deqit/PhilipsPM2528/Data/Fotos (JosVanDijken)/AC AMPLIFIER N24 (4022 325 7917.3).jpg

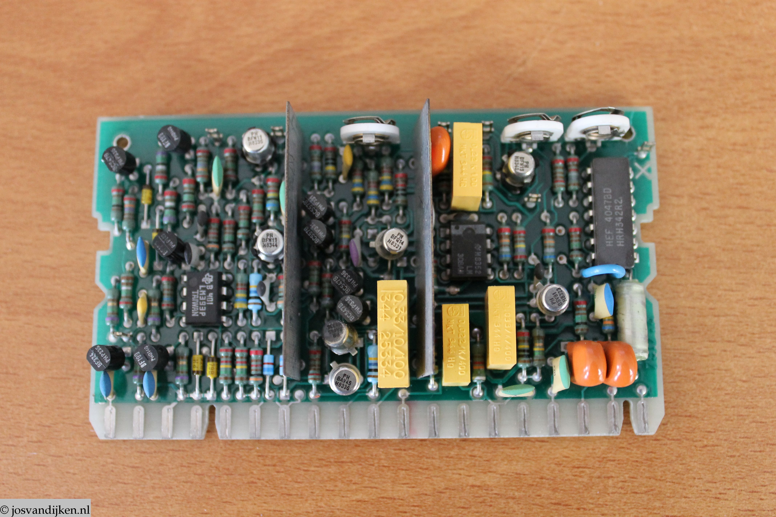
Data/Fotos (JosVanDijken)/AC AMPLIFIER N24 (4022 325 7917.3).jpg
