deqit/PhilipsPM2528/Data/Fotos (JosVanDijken)/ADC ANALOG N21 (4022 325 7911.3).jpg

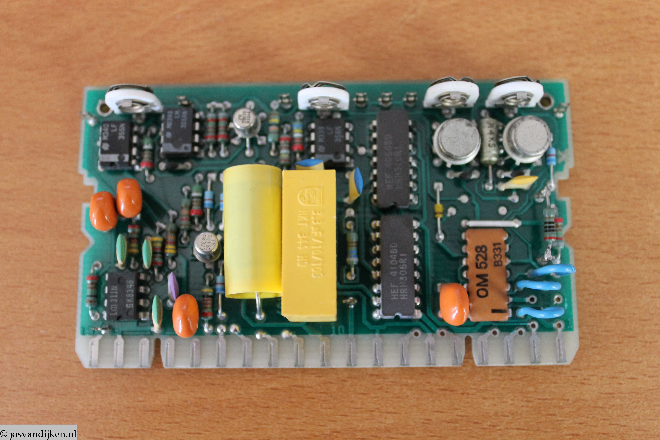
Data/Fotos (JosVanDijken)/ADC ANALOG N21 (4022 325 7911.3).jpg
