deqit/PhilipsPM2528/Data/Fotos (JosVanDijken)/ADC CONTROL N20 (4022 325 7909.4).jpg

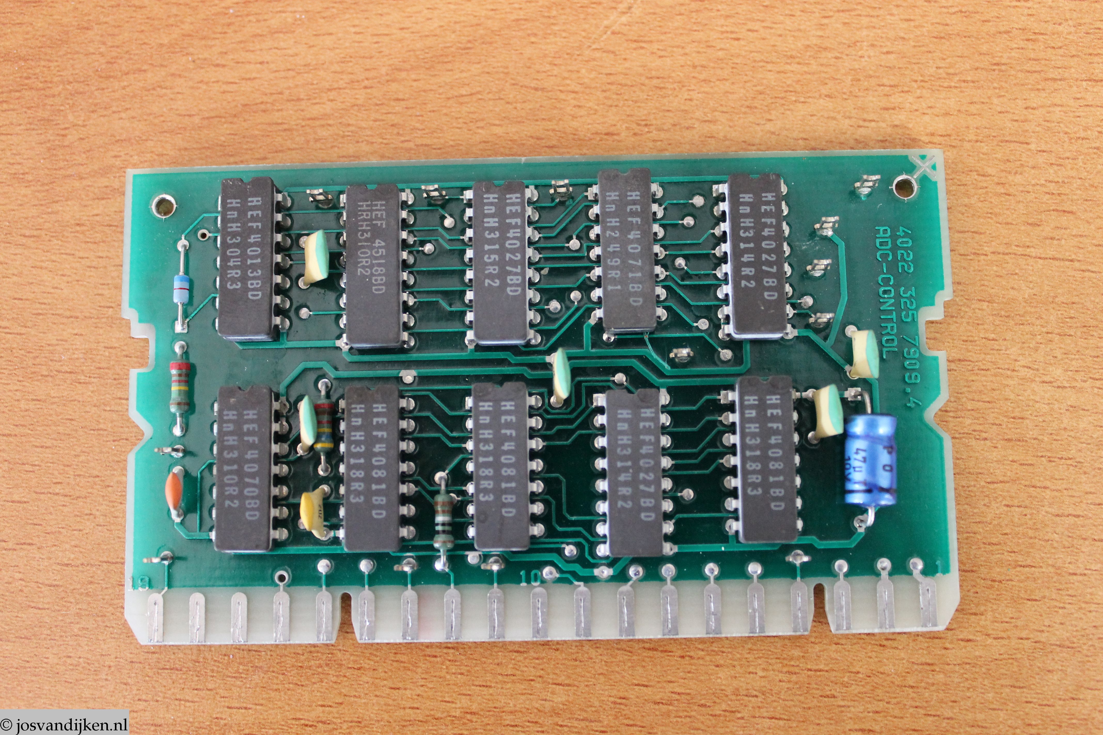
Data/Fotos (JosVanDijken)/ADC CONTROL N20 (4022 325 7909.4).jpg
