deqit/PhilipsPM2528/Data/Fotos (JosVanDijken)/CURRENT SOURCE N23.jpg

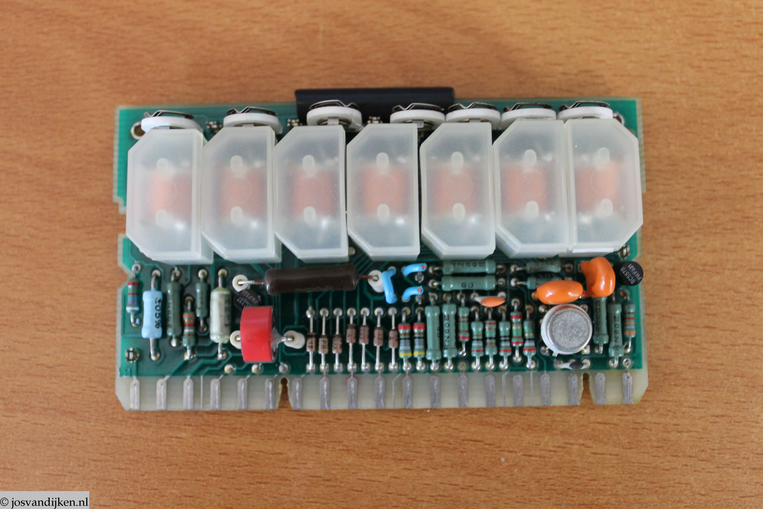
Data/Fotos (JosVanDijken)/CURRENT SOURCE N23.jpg
