deqit/PhilipsPM2528/Data/Fotos (JosVanDijken)/DC AMPLIFIER N22 (4022 325 7913.4).jpg

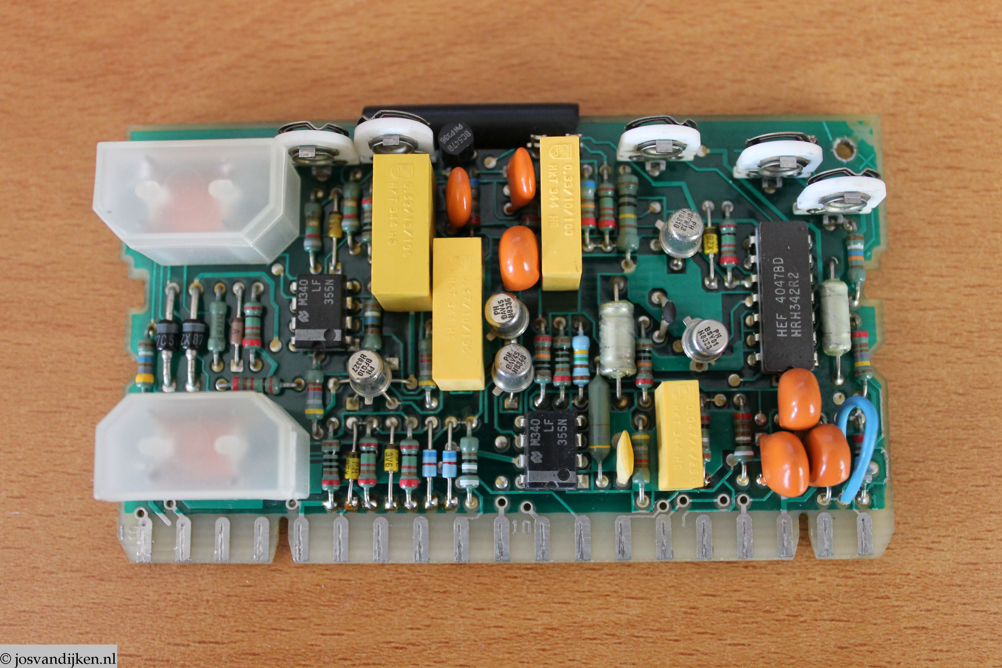
Data/Fotos (JosVanDijken)/DC AMPLIFIER N22 (4022 325 7913.4).jpg
