deqit/PhilipsPM2528/Data/Fotos (JosVanDijken)/GALVANIC SEPERATION N30 (4022 325 7927.3).jpg

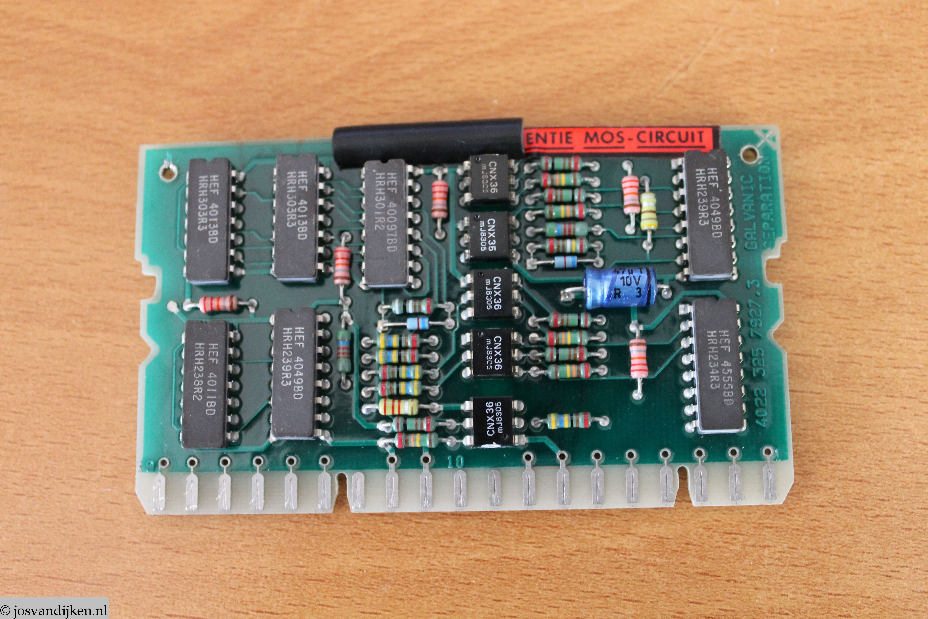
Data/Fotos (JosVanDijken)/GALVANIC SEPERATION N30 (4022 325 7927.3).jpg
