deqit/PhilipsPM2528/Data/Fotos (JosVanDijken)/IEC INTERFACE PM9291(4022 325 7931.4)_back.jpg

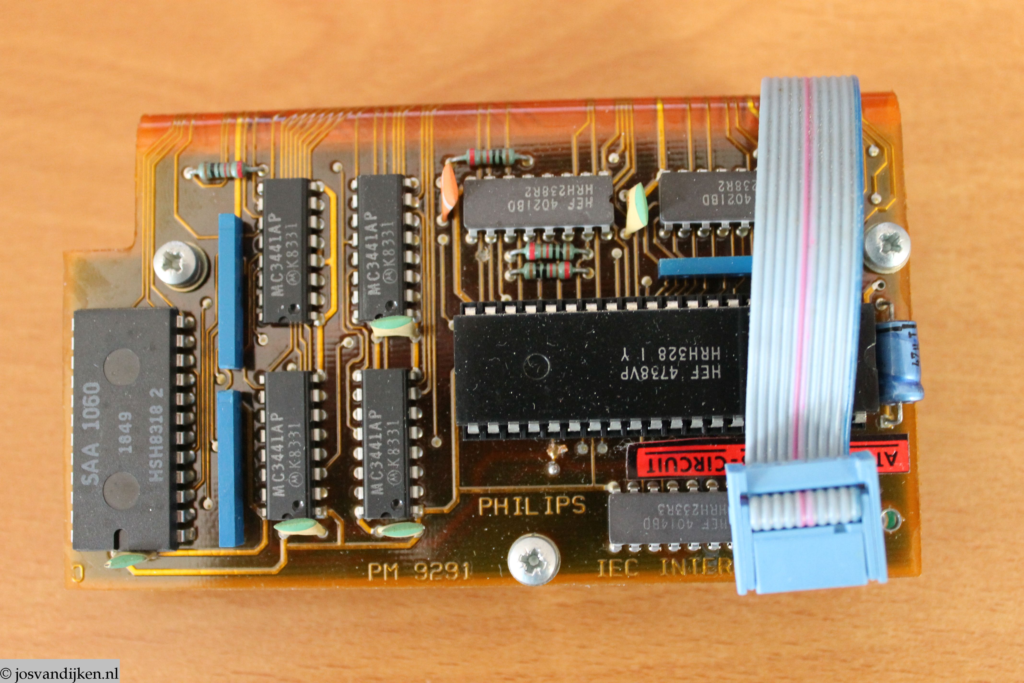
Data/Fotos (JosVanDijken)/IEC INTERFACE PM9291(4022 325 7931.4)_back.jpg
