deqit/PhilipsPM2528/Data/Fotos (JosVanDijken)/IMG_6188.jpg

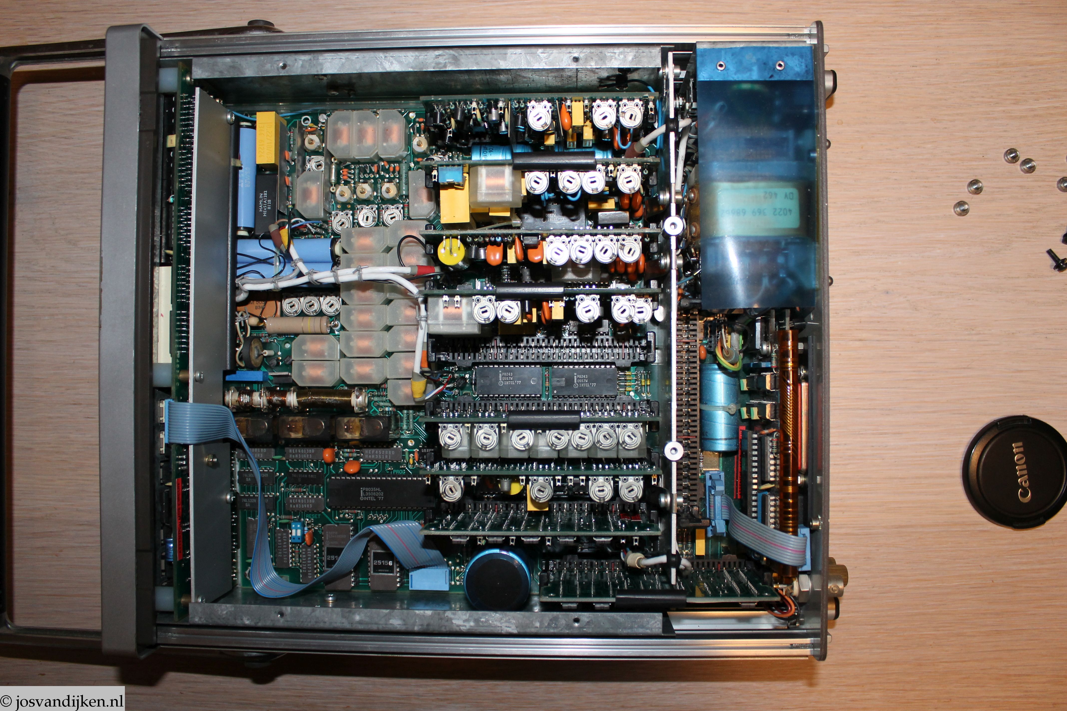
Data/Fotos (JosVanDijken)/IMG_6188.jpg
