deqit/PhilipsPM2528/Data/Fotos (JosVanDijken)/MOTHERBOARD N1 (4022 325 7907.4).jpg

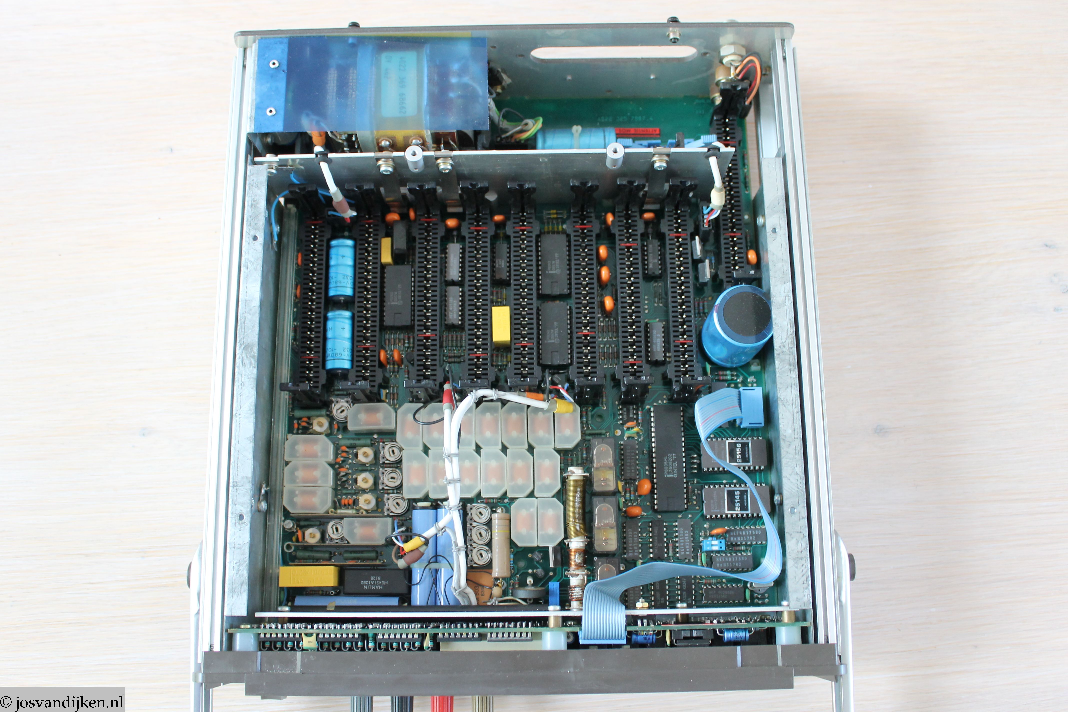
Data/Fotos (JosVanDijken)/MOTHERBOARD N1 (4022 325 7907.4).jpg
