deqit/PhilipsPM2528/Data/Fotos (JosVanDijken)/PEAKDETECTOR PM9259 N27 (4022 325 7923.3).jpg

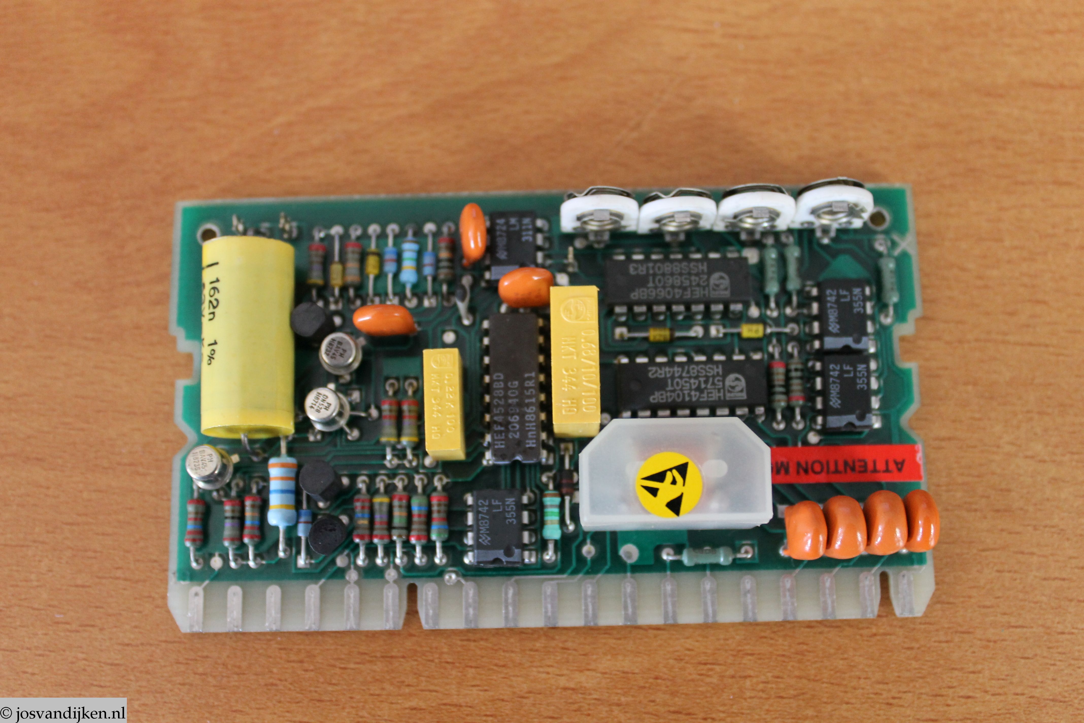
Data/Fotos (JosVanDijken)/PEAKDETECTOR PM9259 N27 (4022 325 7923.3).jpg
