deqit/PhilipsPM2528/Data/Fotos (JosVanDijken)/RMS CONVERTER N25.jpg

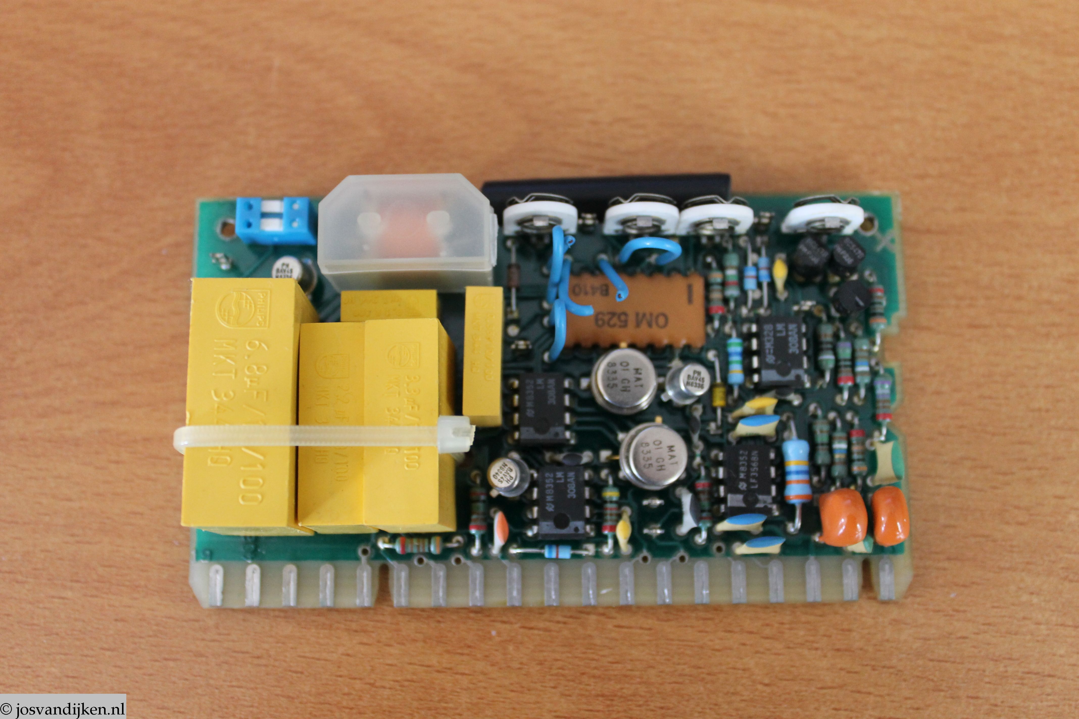
Data/Fotos (JosVanDijken)/RMS CONVERTER N25.jpg
