deqit/PhilipsPM2528/Data/Documentation/Components/BFQ10.pdf

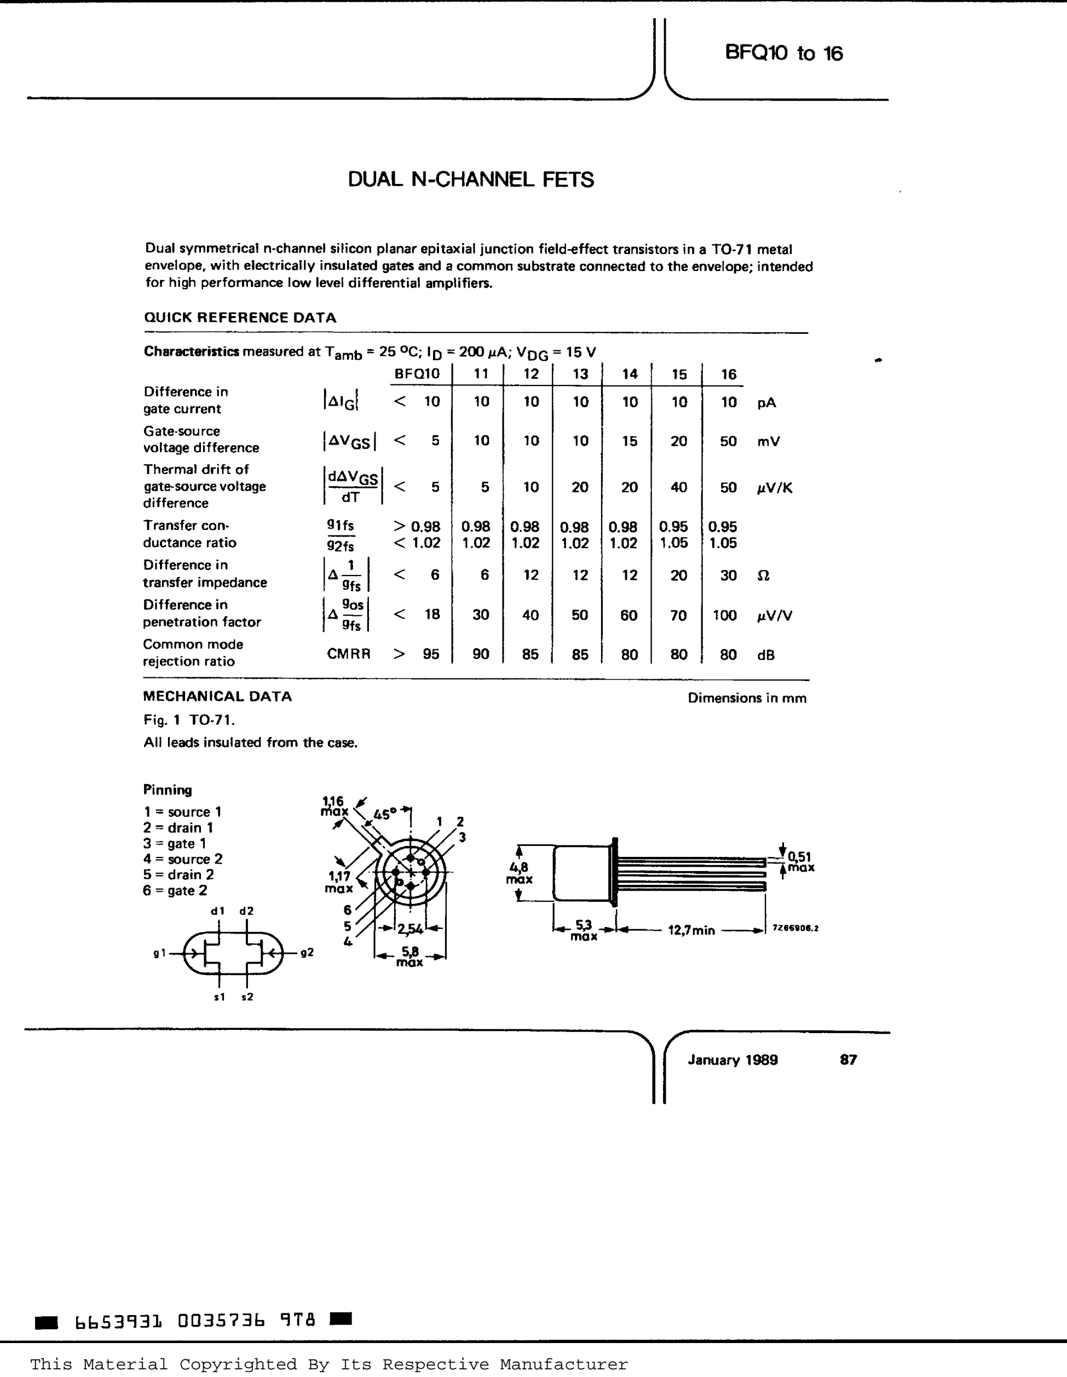
[picture p66: page 1]

This Material Copyrighted By Its Respective Manufacturer

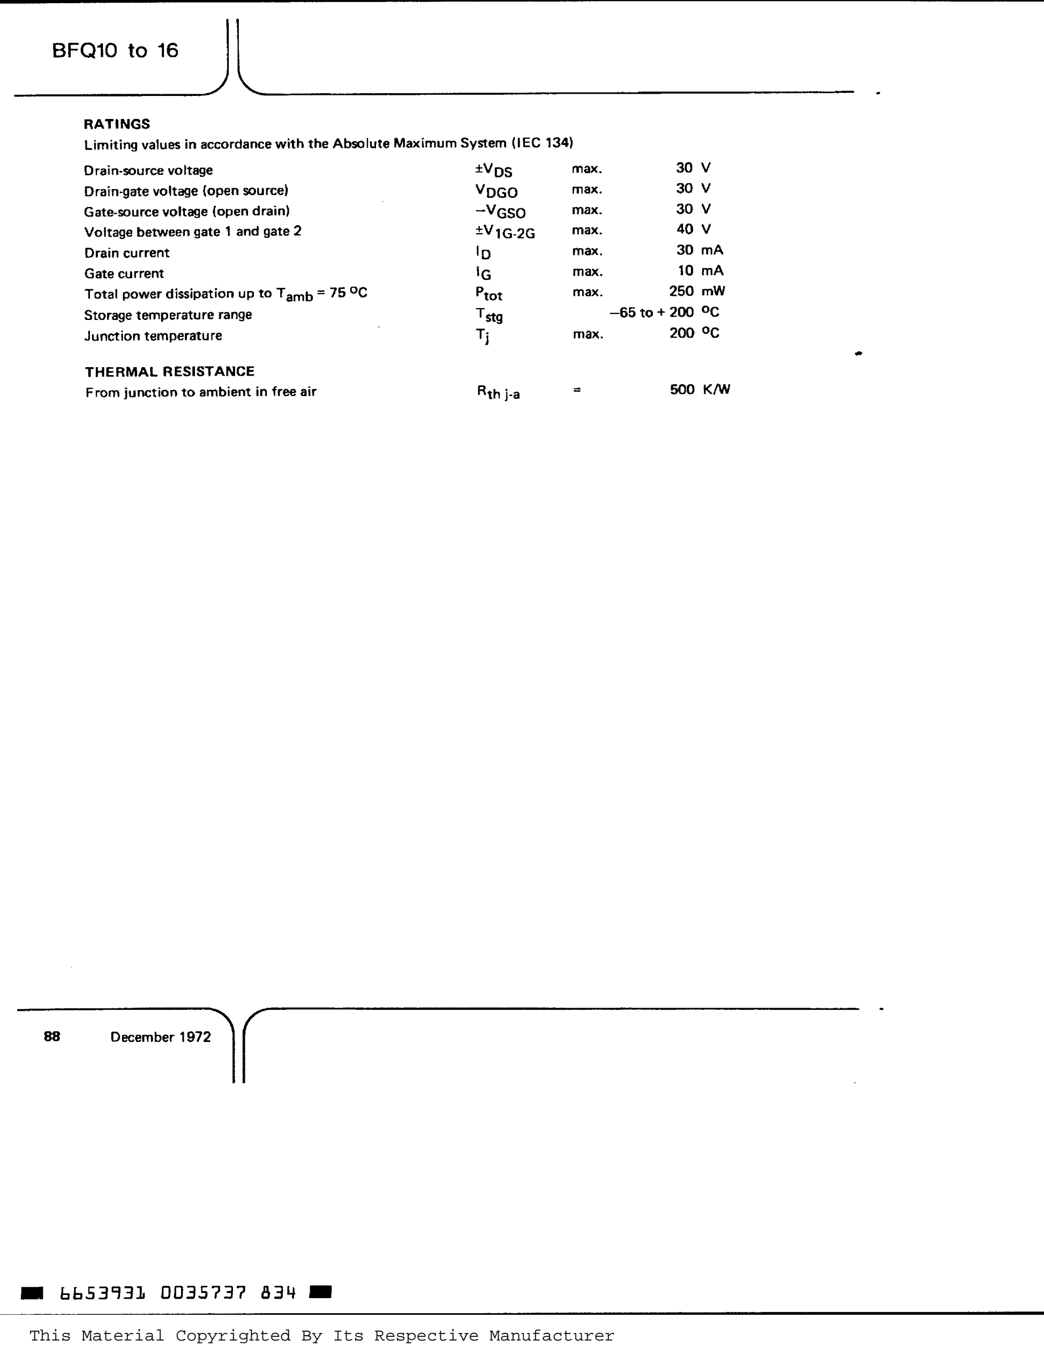
[picture p67: page 2]
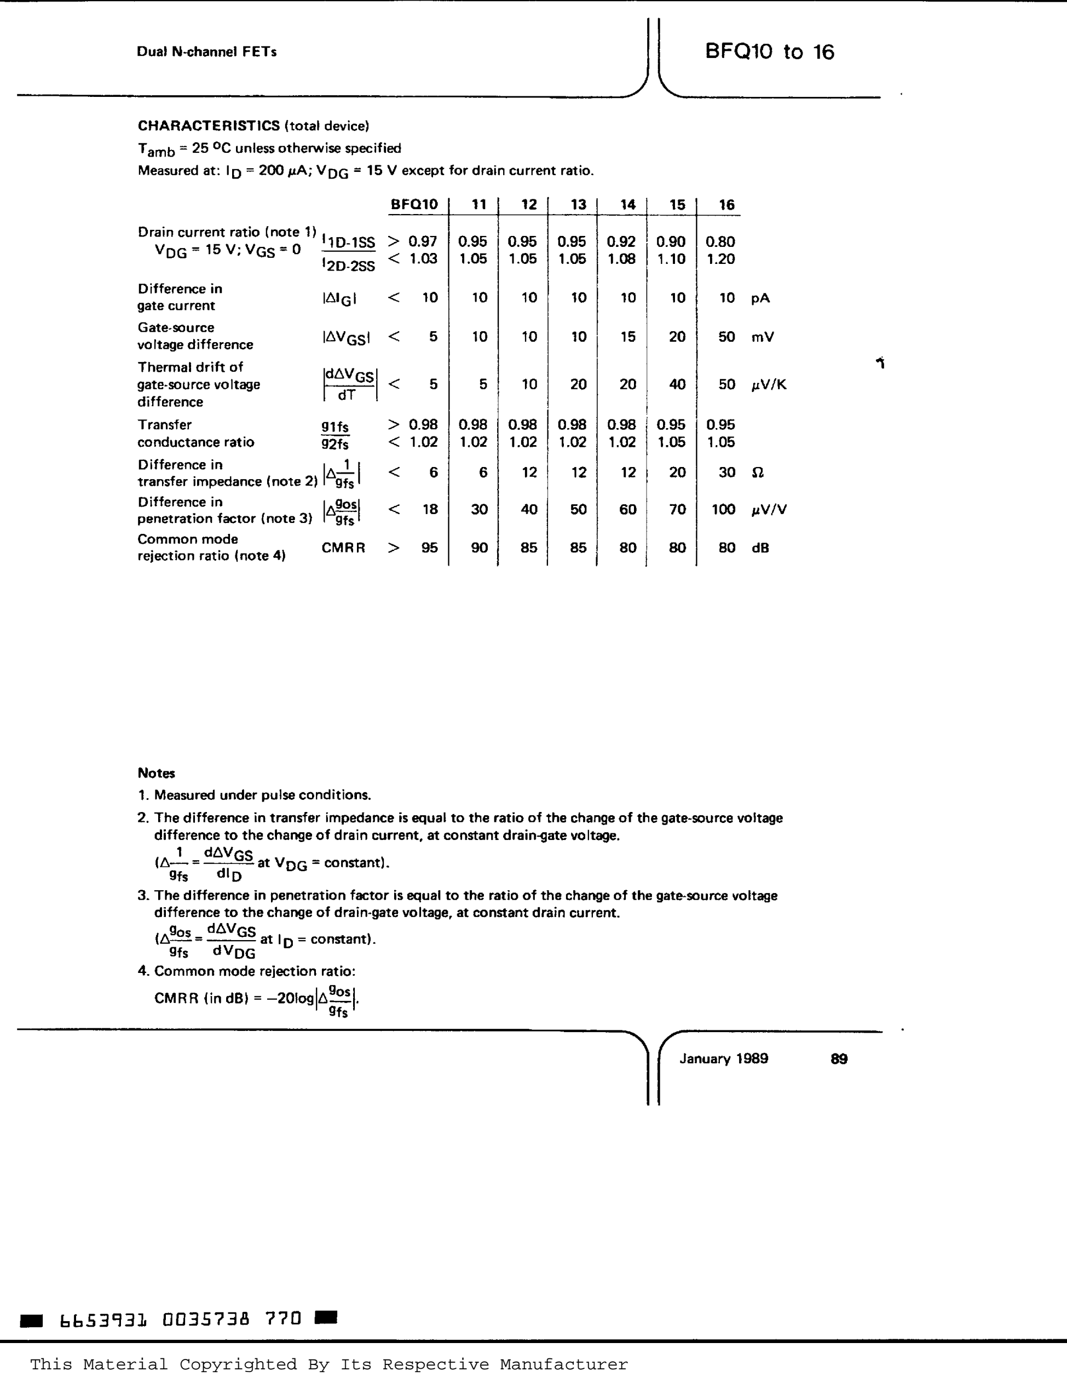
[picture p68: page 3]
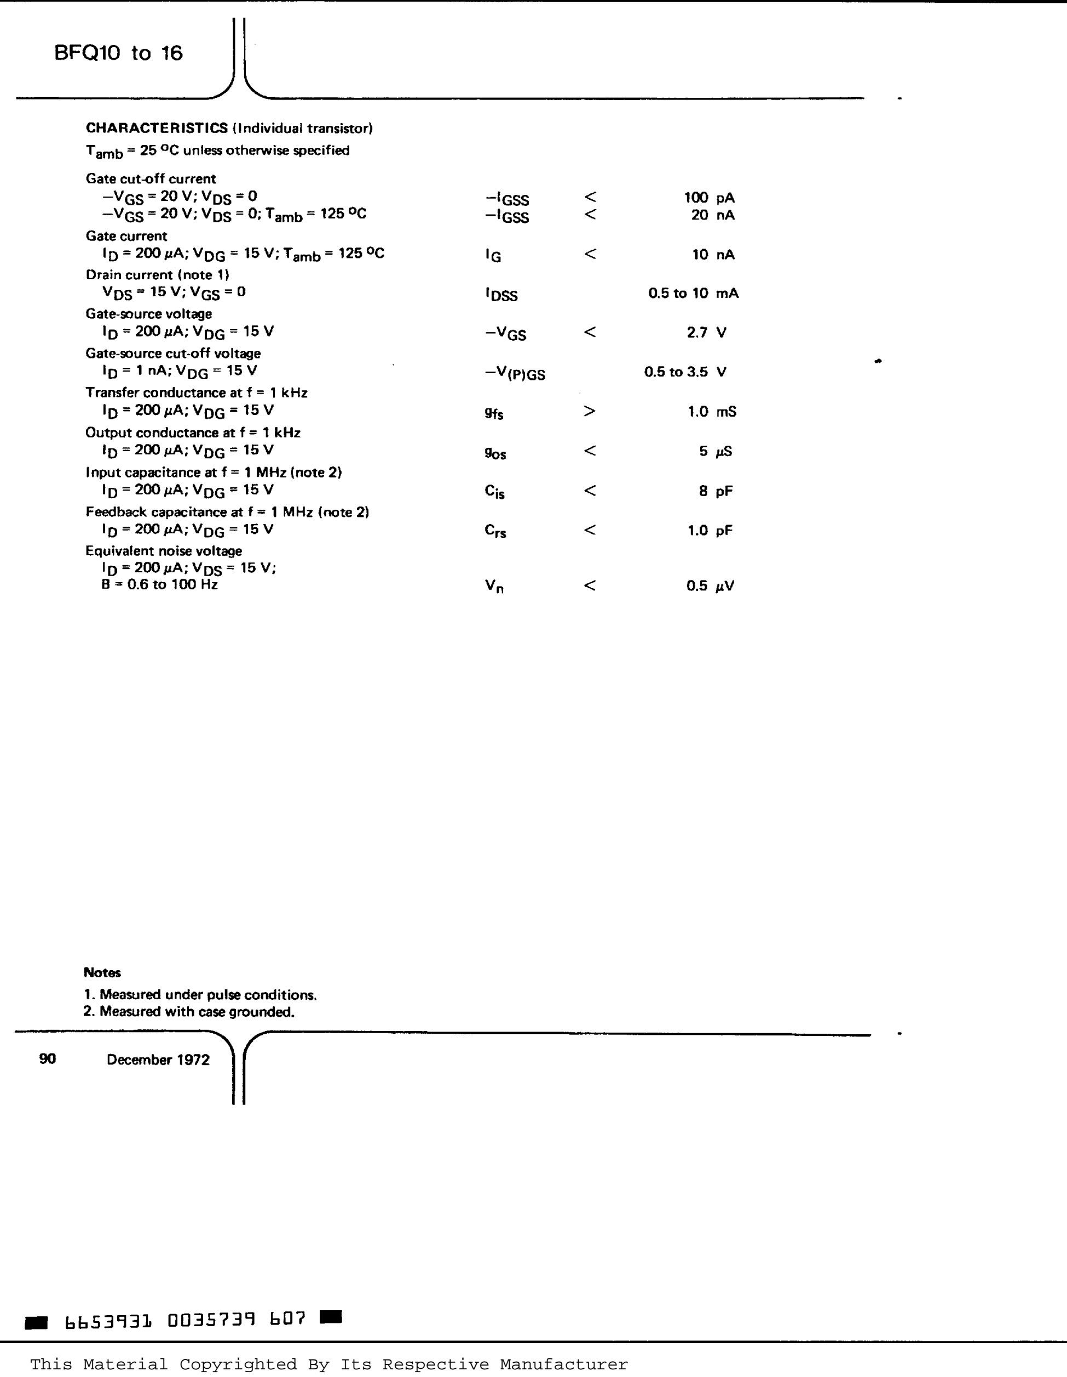
[picture p69: page 4]
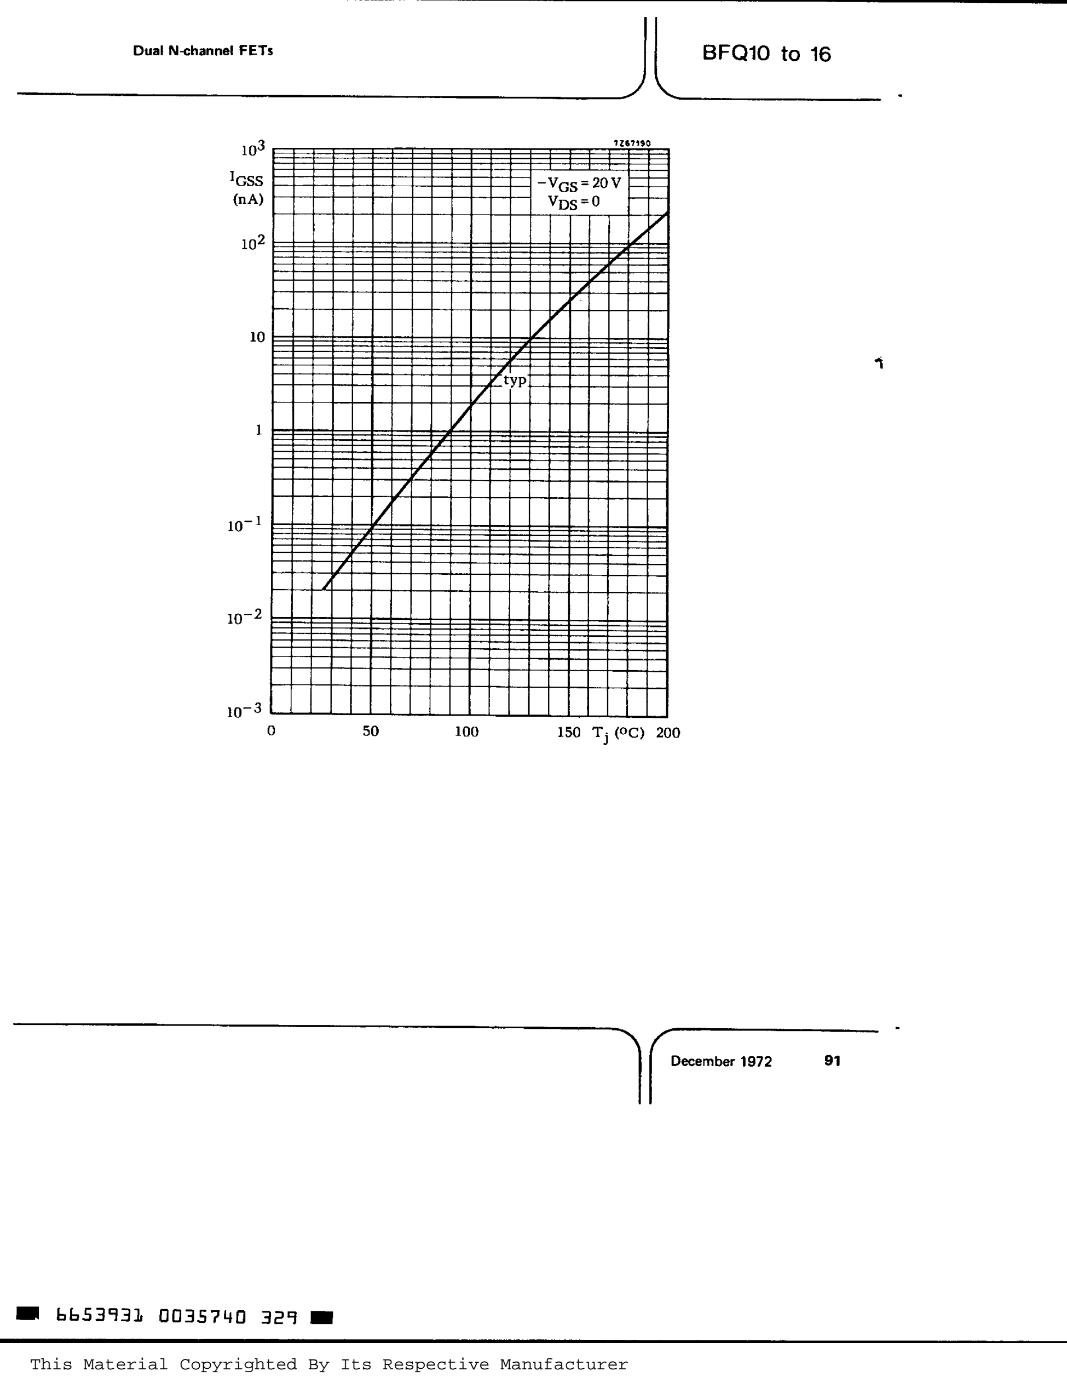
[picture p70: page 5]
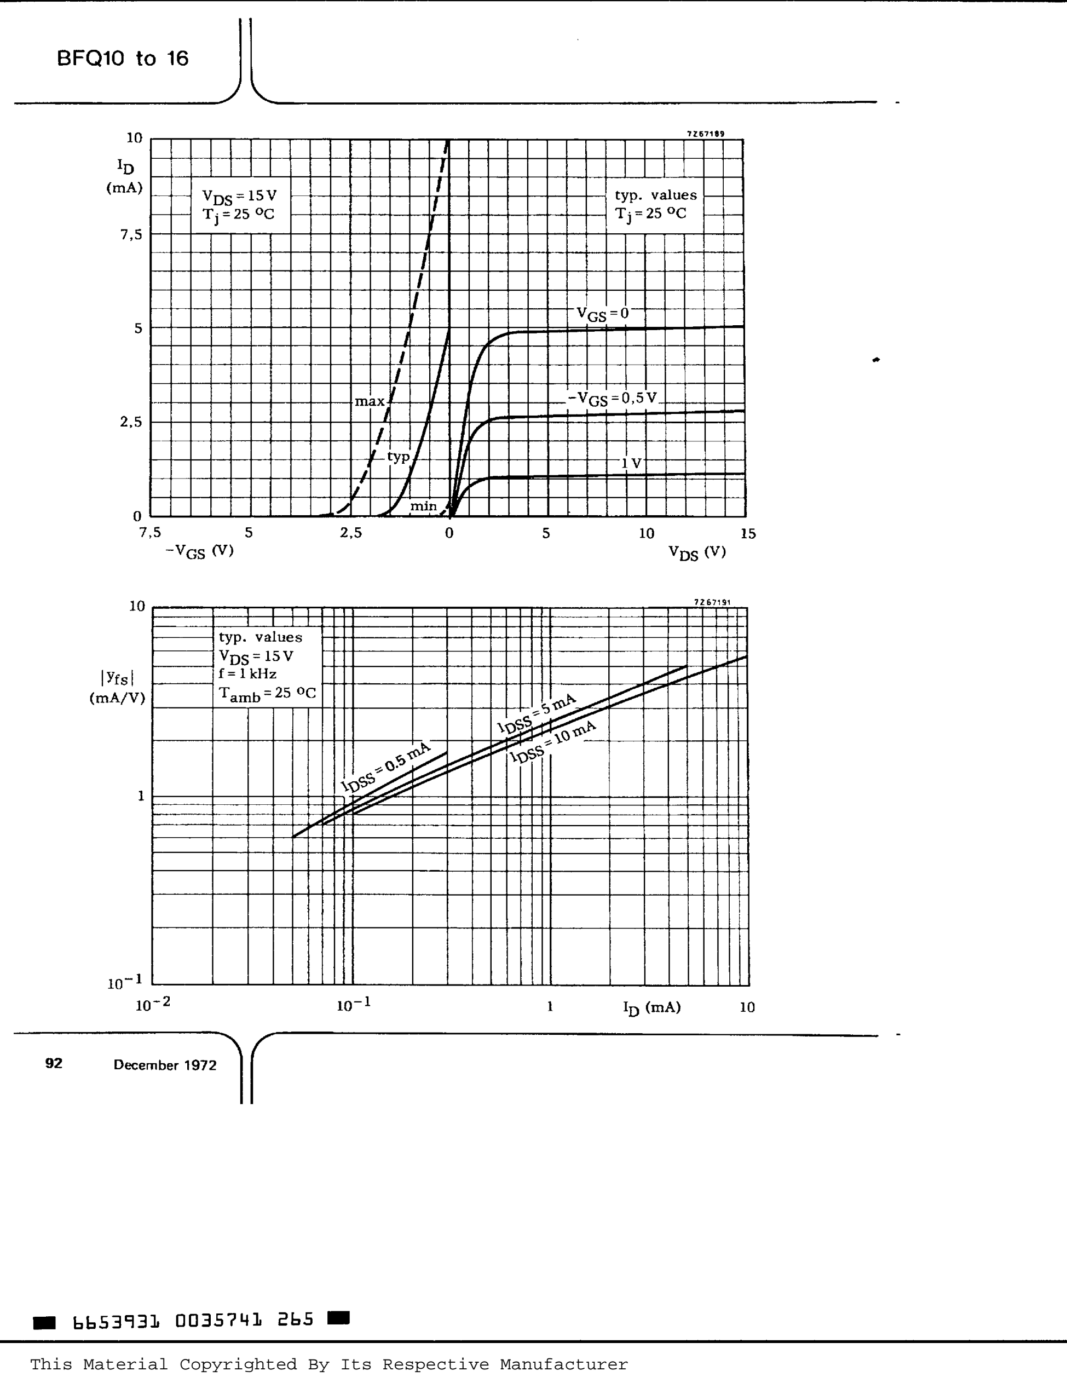
[picture p71: page 6]
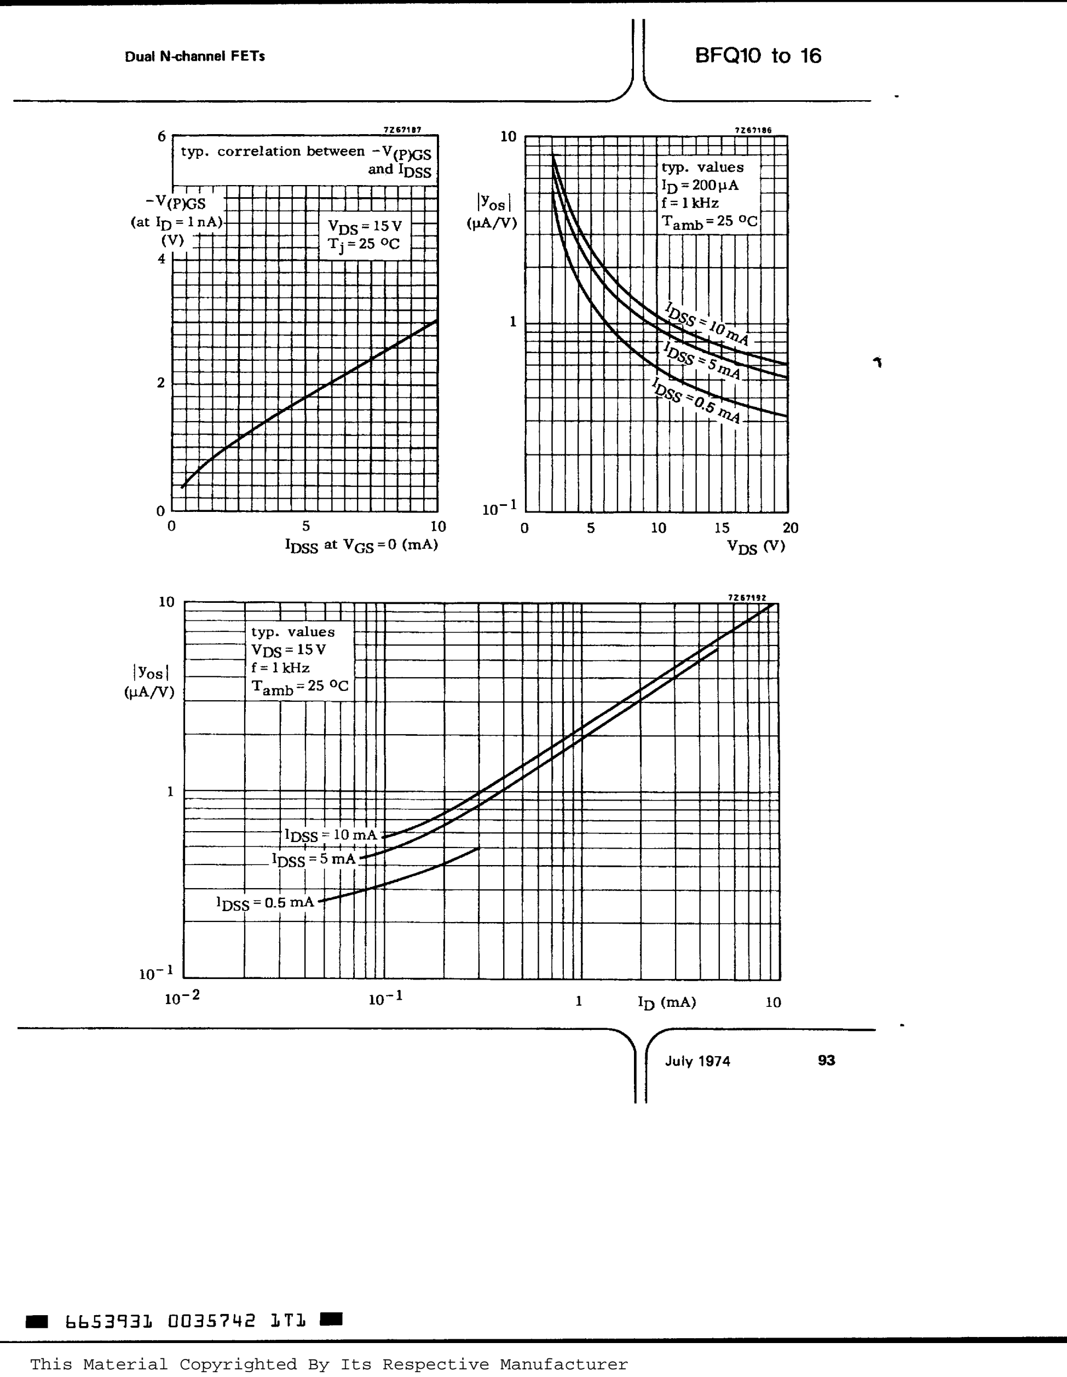
[picture p72: page 7]
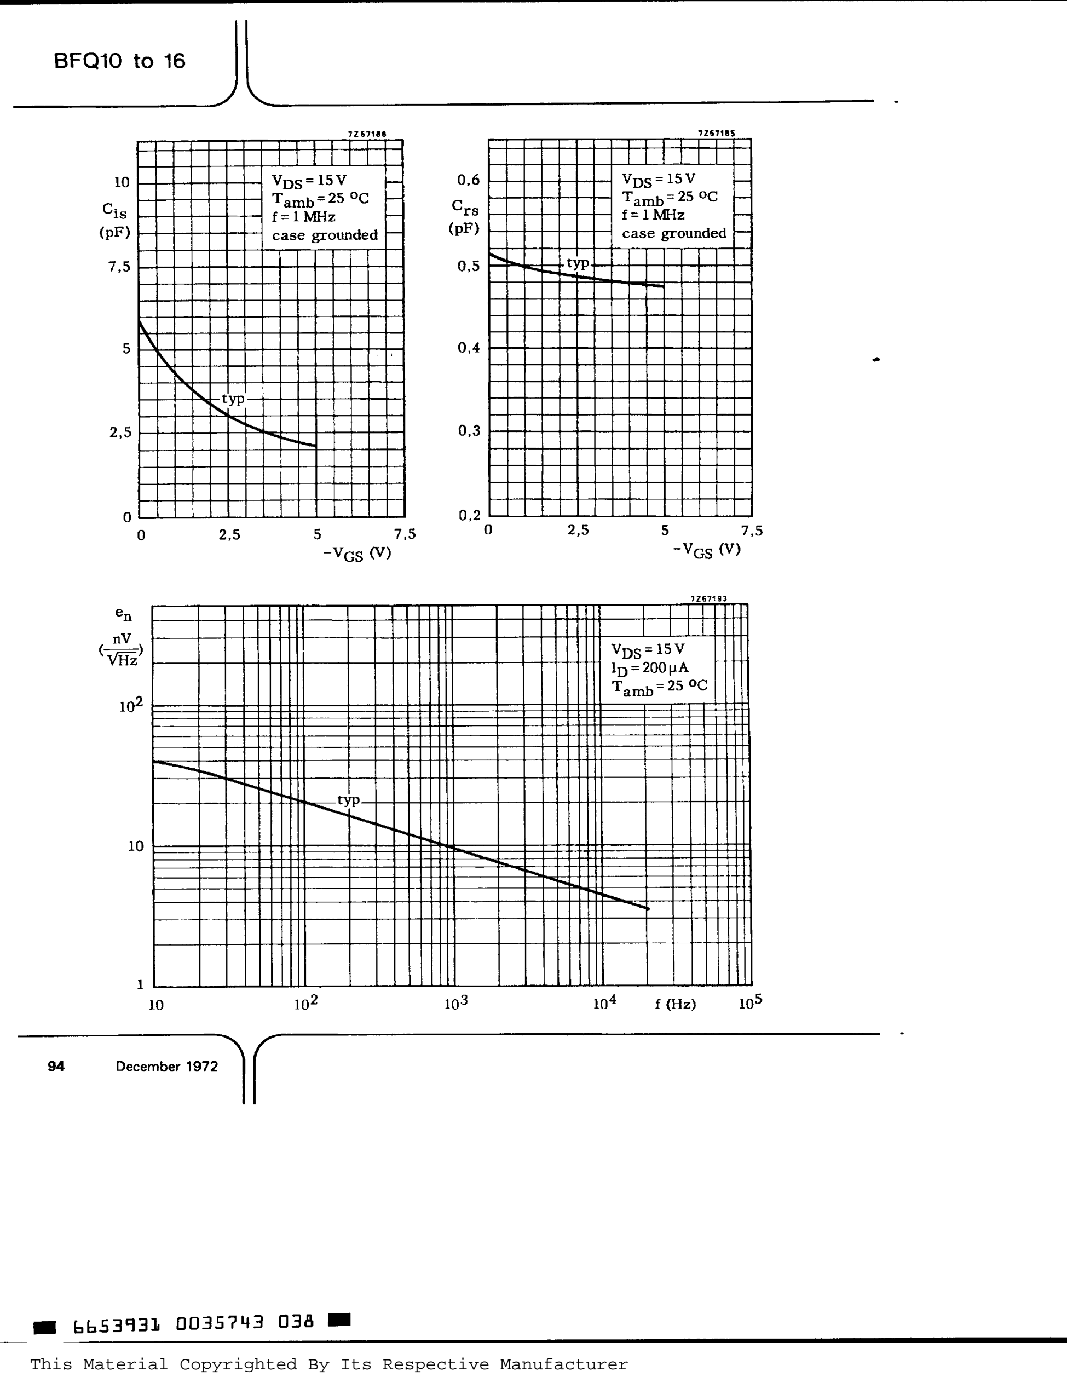
[picture p73: page 8]
