deqit/PhilipsPM2528/Data/Documentation/Components/BSV81.pdf

This Material Copyrighted By Its Respective Manufacturer

# Datasheet.Online

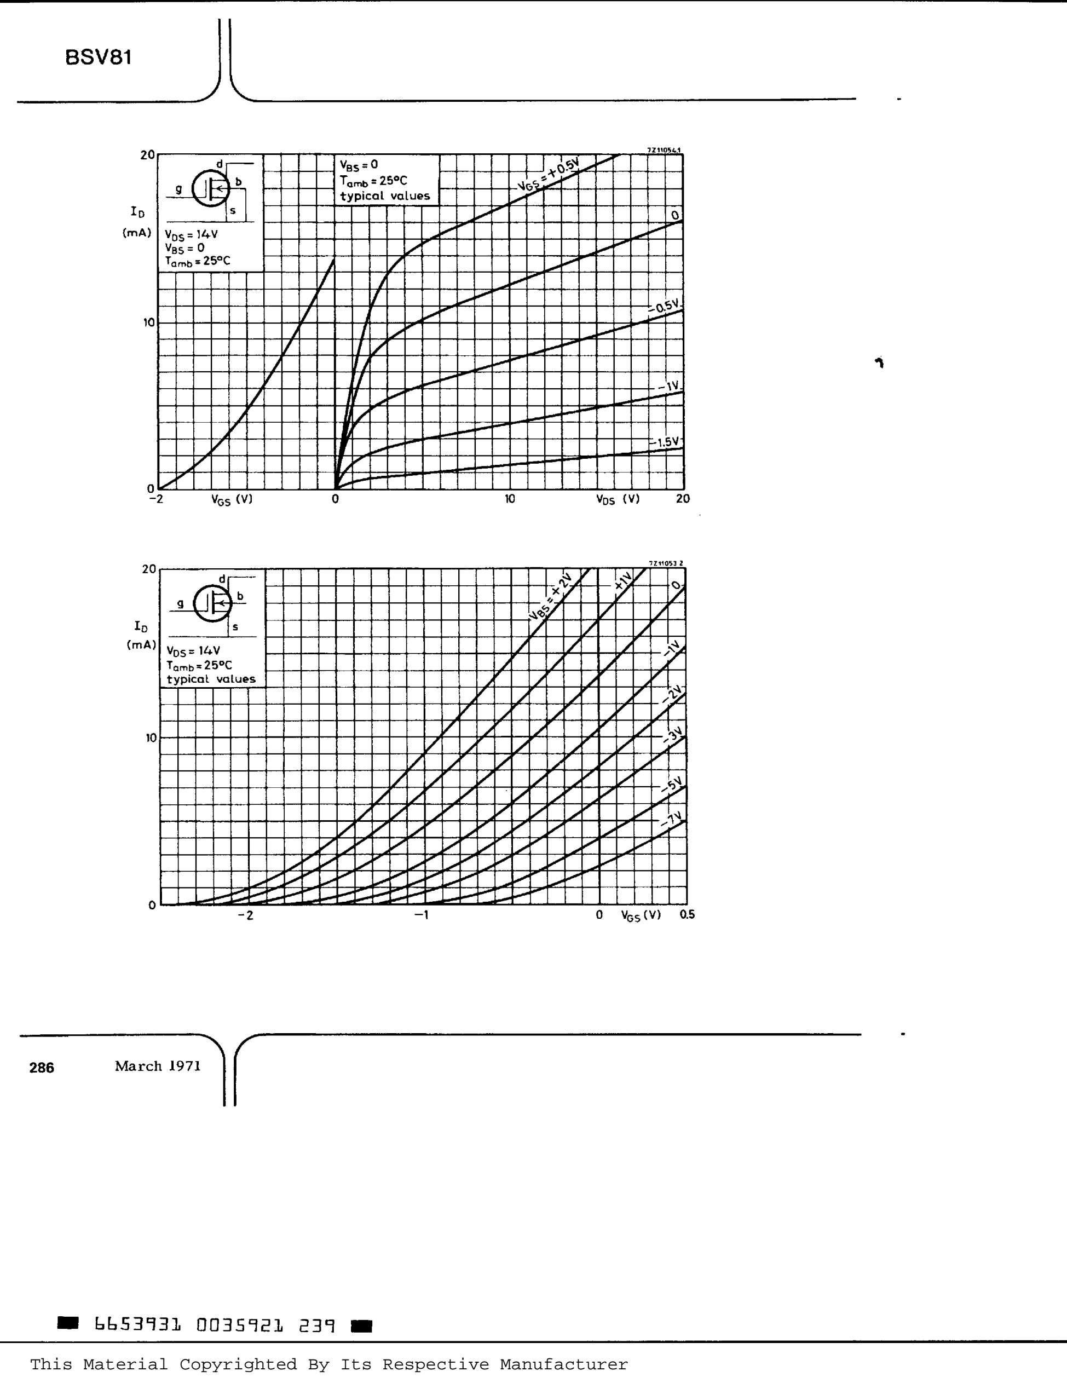
[picture p74: page 4]
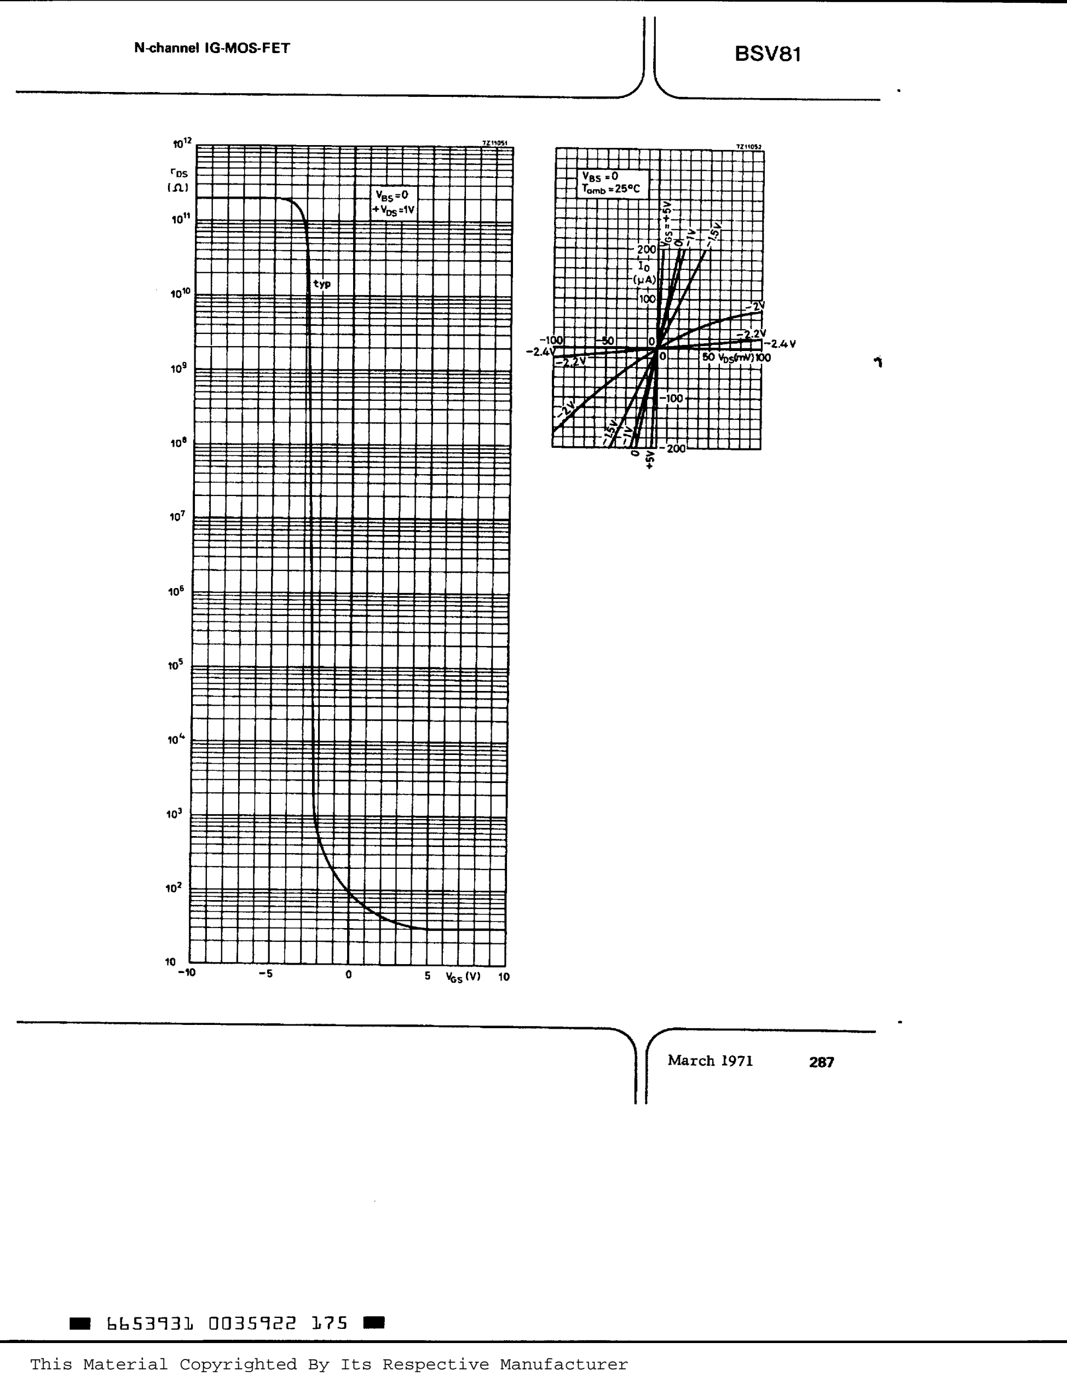
[picture p75: page 5]
