deqit/PhilipsPM2528/N23_CurrentSource/N23_CurrentSource.kicad_sch

## KiCad design N23_CurrentSource/N23_CurrentSource.kicad_sch (2025-07-24)

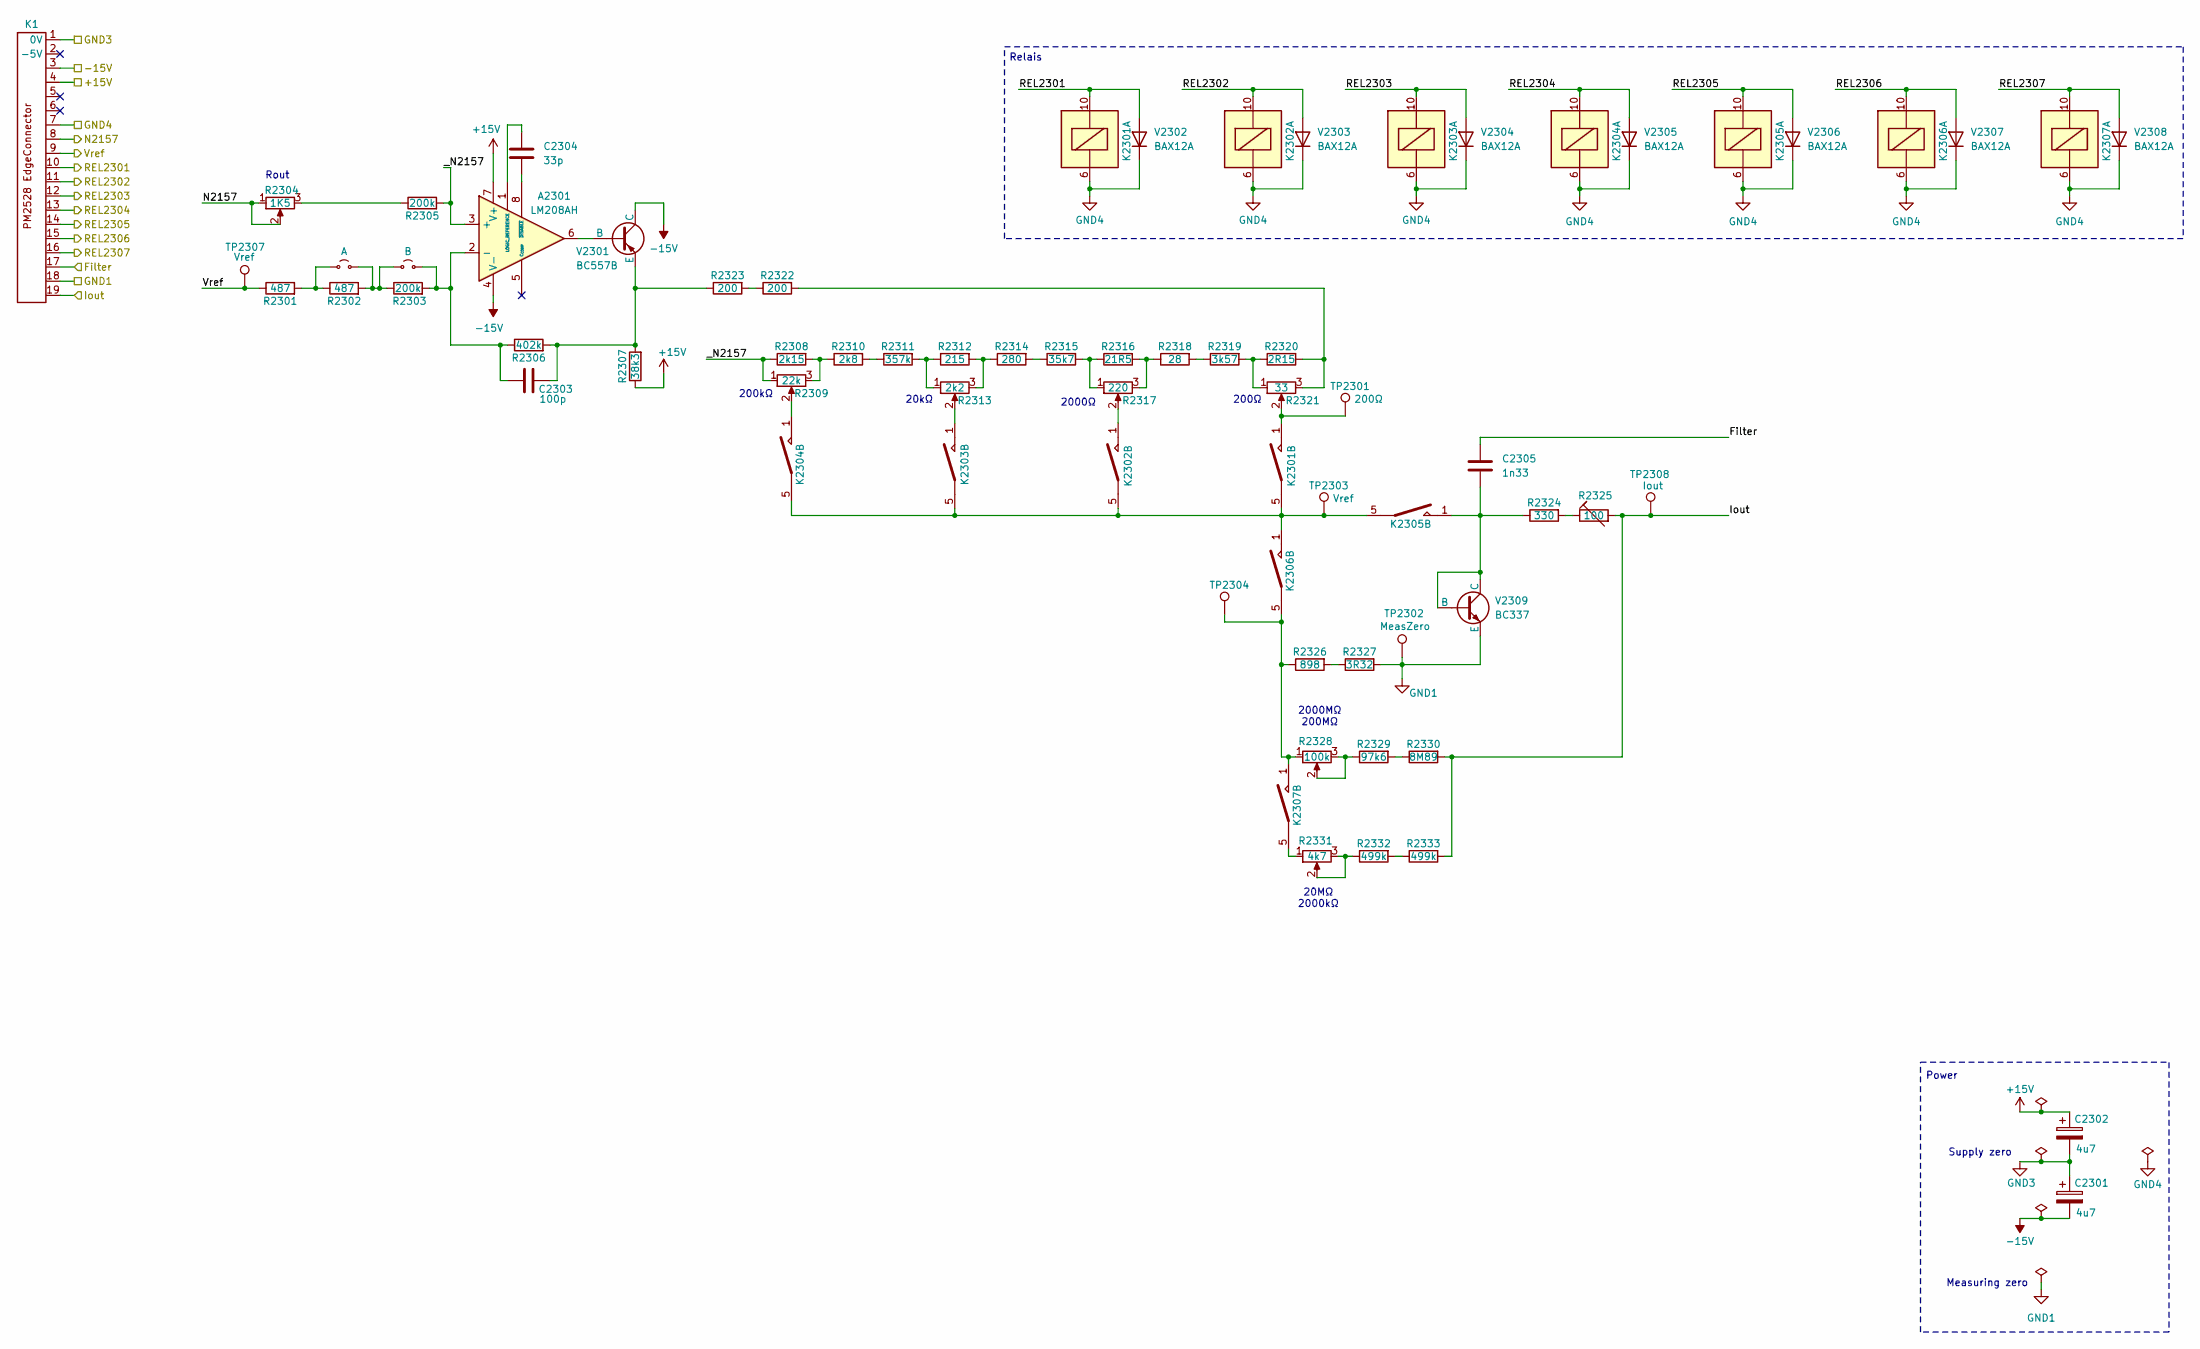
[picture p92: schematic N23_CurrentSource.kicad_sch]

Parts:
A2301: LM208AH; TO-99-8
C2301, C2302: 4u7; C_Rect_L26.5mm_W8.5mm_P22.50mm_MKS4
C2303: 100p; C_Rect_L26.5mm_W8.5mm_P22.50mm_MKS4
C2304: 33p; C_Rect_L26.5mm_W8.5mm_P22.50mm_MKS4
C2305: 1n33; C_Rect_L26.5mm_W8.5mm_P22.50mm_MKS4
JP1: A; TestPoint_Bridge_Pitch5.08mm_Drill0.7mm
JP2: B; TestPoint_Bridge_Pitch5.08mm_Drill0.7mm
K1: PM2528_RiserCardConnector
K2301, K2302, K2303, K2304, K2305, K2306, K2307: Reed relay assy
R2301, R2302: 487; R_Axial_DIN0207_L6.3mm_D2.5mm_P10.16mm_Horizontal
R2303, R2305: 200k; R_Axial_DIN0207_L6.3mm_D2.5mm_P10.16mm_Horizontal
R2304: 1K5; Potentiometer horizontal ceramic
R2306: 402k; R_Axial_DIN0207_L6.3mm_D2.5mm_P10.16mm_Horizontal
R2307: 38k3; R_Axial_DIN0207_L6.3mm_D2.5mm_P10.16mm_Horizontal
R2308: 2k15; R_Axial_DIN0207_L6.3mm_D2.5mm_P10.16mm_Horizontal
R2309: 22k; Potentiometer horizontal ceramic
R2310: 2k8; R_Axial_DIN0207_L6.3mm_D2.5mm_P10.16mm_Horizontal
R2311: 357k; R_Axial_DIN0207_L6.3mm_D2.5mm_P10.16mm_Horizontal
R2312: 215; R_Axial_DIN0207_L6.3mm_D2.5mm_P10.16mm_Horizontal
R2313: 2k2; Potentiometer horizontal ceramic
R2314: 280; R_Axial_DIN0207_L6.3mm_D2.5mm_P10.16mm_Horizontal
R2315: 35k7; R_Axial_DIN0207_L6.3mm_D2.5mm_P10.16mm_Horizontal
R2316: 21R5; R_Axial_DIN0207_L6.3mm_D2.5mm_P10.16mm_Horizontal
R2317: 220; Potentiometer horizontal ceramic
R2318: 28; R_Axial_DIN0207_L6.3mm_D2.5mm_P10.16mm_Horizontal
R2319: 3k57; R_Axial_DIN0207_L6.3mm_D2.5mm_P10.16mm_Horizontal
R2320: 2R15; R_Axial_DIN0207_L6.3mm_D2.5mm_P10.16mm_Horizontal
R2321: 33; Potentiometer horizontal ceramic
R2322, R2323: 200; R_Axial_DIN0207_L6.3mm_D2.5mm_P10.16mm_Horizontal
R2324: 330; R_Axial_DIN0207_L6.3mm_D2.5mm_P10.16mm_Horizontal
R2325: 100; R_Axial_DIN0207_L6.3mm_D2.5mm_P10.16mm_Horizontal
R2326: 898; R_Axial_DIN0207_L6.3mm_D2.5mm_P10.16mm_Horizontal
R2327: 3R32; R_Axial_DIN0207_L6.3mm_D2.5mm_P10.16mm_Horizontal
R2328: 100k; Potentiometer horizontal ceramic
R2329: 97k6; R_Axial_DIN0207_L6.3mm_D2.5mm_P10.16mm_Horizontal
R2330: 8M89; R_Axial_DIN0207_L6.3mm_D2.5mm_P10.16mm_Horizontal
R2331: 4k7; Potentiometer horizontal ceramic
R2332, R2333: 499k; R_Axial_DIN0207_L6.3mm_D2.5mm_P10.16mm_Horizontal
TP2301: 200Ω; PinHeader_1x01_P1.00mm_Vertical
TP2302: MeasZero; PinHeader_1x01_P1.00mm_Vertical
TP2303, TP2307: Vref; PinHeader_1x01_P1.00mm_Vertical
TP2304: PinHeader_1x01_P1.00mm_Vertical
TP2308: Iout; PinHeader_1x01_P1.00mm_Vertical
V2301: BC557B; TO-92
V2302, V2303, V2304, V2305, V2306, V2307, V2308: BAX12A; D_DO-41_SOD81_P10.16mm_Horizontal
V2309: BC337; TO-92

Connections:
+15V: A2301.7 (V+), C2302.1, K1.4, R2307.1
-15V: A2301.4 (V-), C2301.2, K1.3, V2301.1 (C)
Filter: C2305.2, K1.17
GND1: K1.18, R2327.2, TP2302.1, V2309.3 (E)
GND3: C2301.1, C2302.2, K1.1 (0V)
GND4: K1.7, K2301.6, K2302.6, K2303.6, K2304.6, K2305.6, K2306.6, K2307.6, V2302.1 (K), V2303.1 (K), V2304.1 (K), V2305.1 (K), V2306.1 (K), V2307.1 (K), V2308.1 (K)
Iout: K1.19, R2325.2, R2330.2, R2333.2, TP2308.1
N2157: K1.8, R2304.1, R2304.2
unnamed: A2301.1 (LOGIC_REFERENCE), C2304.1
unnamed: A2301.2 (-), C2303.2, JP2.2 (B), R2303.2, R2306.1
unnamed: A2301.6, V2301.2 (B)
unnamed: A2301.8 (~DISABLE), C2304.2
unnamed: C2303.1, R2306.2, R2307.2, R2323.1, V2301.3 (E)
unnamed: C2305.1, K2305.1, R2324.1, V2309.1 (C), V2309.2 (B)
unnamed: JP1.1 (A), R2301.2, R2302.1
unnamed: JP1.2 (B), JP2.1 (A), R2302.2, R2303.1
unnamed: K2301.1, R2321.2, TP2301.1
unnamed: K2301.5, K2302.5, K2303.5, K2304.5, K2305.5, K2306.1, TP2303.1
unnamed: K2302.1, R2317.2
unnamed: K2303.1, R2313.2
unnamed: K2304.1, R2309.2
unnamed: K2306.5, K2307.1, R2326.1, R2328.1, TP2304.1
unnamed: K2307.5, R2331.1
unnamed: R2304.3, R2305.1
unnamed: R2308.2, R2309.3, R2310.1
unnamed: R2310.2, R2311.1
unnamed: R2311.2, R2312.1, R2313.1
unnamed: R2312.2, R2313.3, R2314.1
unnamed: R2314.2, R2315.1
unnamed: R2315.2, R2316.1, R2317.1
unnamed: R2316.2, R2317.3, R2318.1
unnamed: R2318.2, R2319.1
unnamed: R2319.2, R2320.1, R2321.1
unnamed: R2320.2, R2321.3, R2322.2
unnamed: R2322.1, R2323.2
unnamed: R2324.2, R2325.1
unnamed: R2326.2, R2327.1
unnamed: R2328.2, R2328.3, R2329.1
unnamed: R2329.2, R2330.1
unnamed: R2331.2, R2331.3, R2332.1
unnamed: R2332.2, R2333.1
REL2301: K1.10, K2301.10, V2302.2 (A)
REL2302: K1.11, K2302.10, V2303.2 (A)
REL2303: K1.12, K2303.10, V2304.2 (A)
REL2304: K1.13, K2304.10, V2305.2 (A)
REL2305: K1.14, K2305.10, V2306.2 (A)
REL2306: K1.15, K2306.10, V2307.2 (A)
REL2307: K1.16, K2307.10, V2308.2 (A)
Vref: K1.9, R2301.1, TP2307.1
_N2157: A2301.3 (+), R2305.2, R2308.1, R2309.1

Notes on the sheet:
200Ω
Power
Measuring zero
20kΩ
2000MΩ 200MΩ
200kΩ
20MΩ 2000kΩ
Relais
2000Ω
Rout
Supply zero
